nup002/Mathboard/hardware/pcb/kicad/resources/3d_models/xb-msk-103.stp

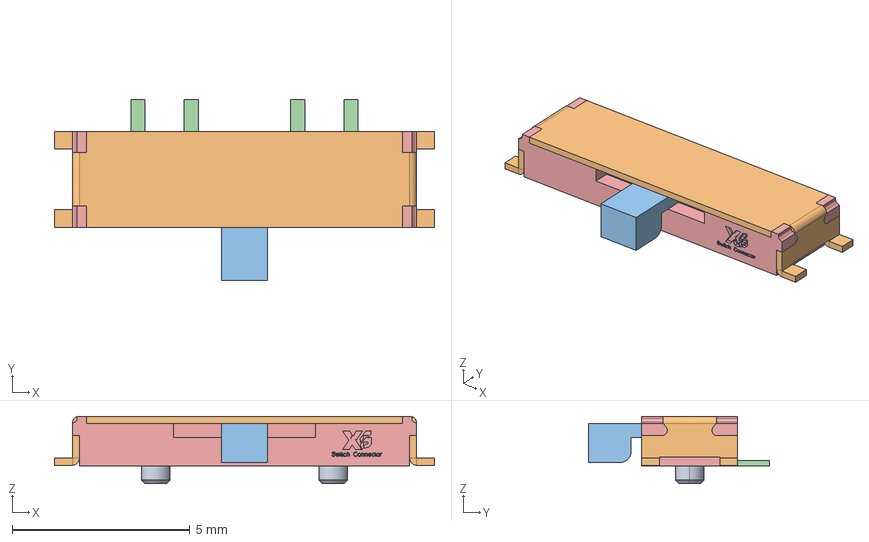
[picture p19: CAD file, 2024-10-21]
hardware/pcb/kicad/resources/3d_models/xb-msk-103.stp
10.7 x 5.10 x 1.90 mm
