nup002/Mathboard/hardware/pcb/kicad/resources/3d_models/3303W-3.step

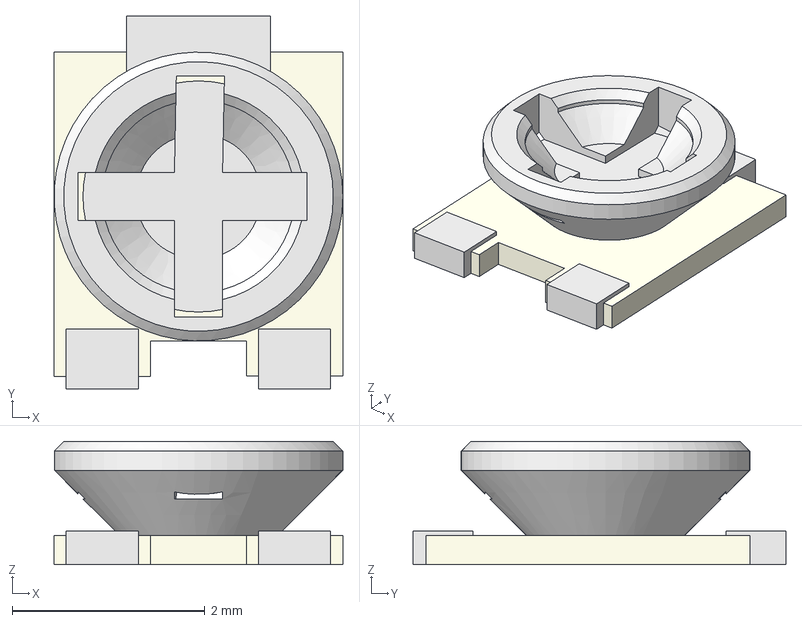
[picture p20: CAD file, 2024-10-21]
hardware/pcb/kicad/resources/3d_models/3303W-3.step
3.00 x 3.88 x 1.28 mm
