nup002/Mathboard/hardware/pcb/kicad/resources/3d_models/WSON8-8x6.STEP

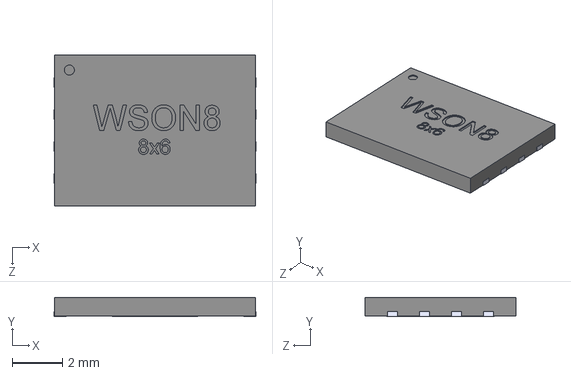
[picture p21: CAD file, 2024-10-21]
hardware/pcb/kicad/resources/3d_models/WSON8-8x6.STEP
8.02 x 0.77 x 6.00 mm
