nup002/Mathboard/hardware/pcb/kicad/resources/3d_models/USB - C inboard.STEP

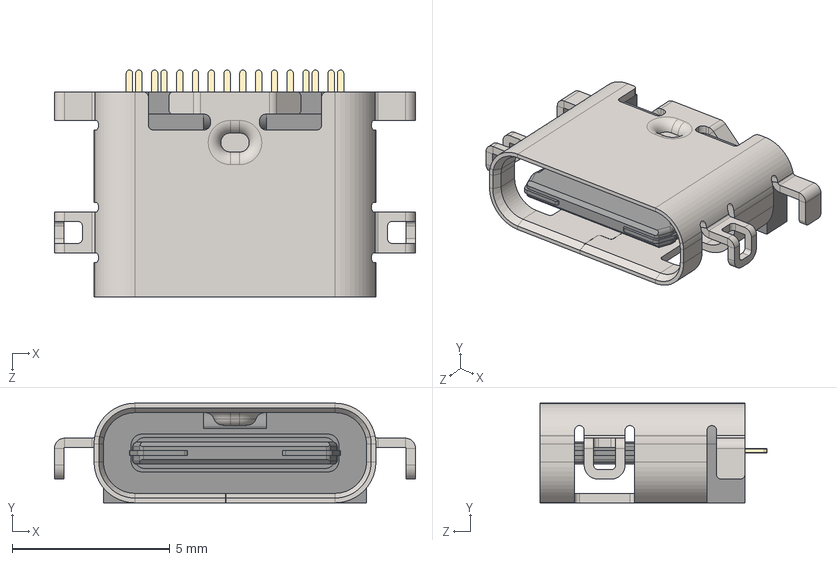
[picture p22: CAD file, 2024-10-01]
hardware/pcb/kicad/resources/3d_models/USB - C inboard.STEP
11.5 x 3.16 x 7.20 mm
USB-C inboard metal
USB-C plastic
