nup002/Mathboard/hardware/pcb/kicad/resources/3d_models/TS-1187A.step

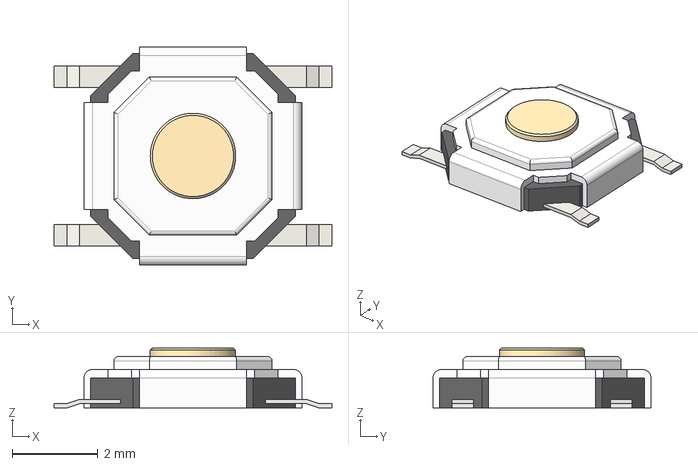
[picture p23: CAD file, 2024-09-27]
hardware/pcb/kicad/resources/3d_models/TS-1187A.step
6.50 x 5.10 x 1.40 mm
