nup002/Mathboard/hardware/pcb/kicad/resources/3d_models/SK6812MINI-E v1.step

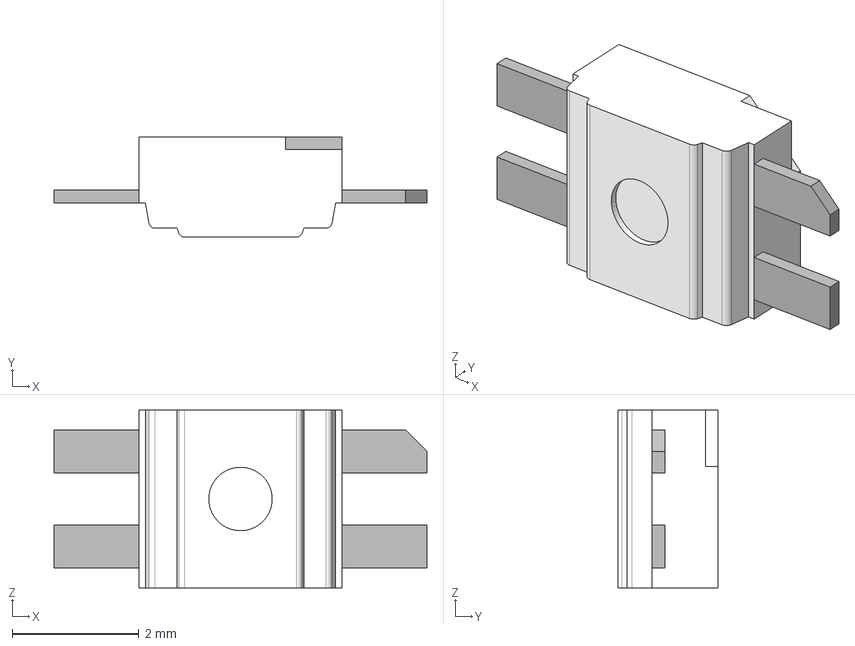
[picture p24: CAD file, 2024-04-30]
hardware/pcb/kicad/resources/3d_models/SK6812MINI-E v1.step
5.88 x 1.58 x 2.80 mm
