nup002/Mathboard/hardware/pcb/kicad/resources/3d_models/ks33.step

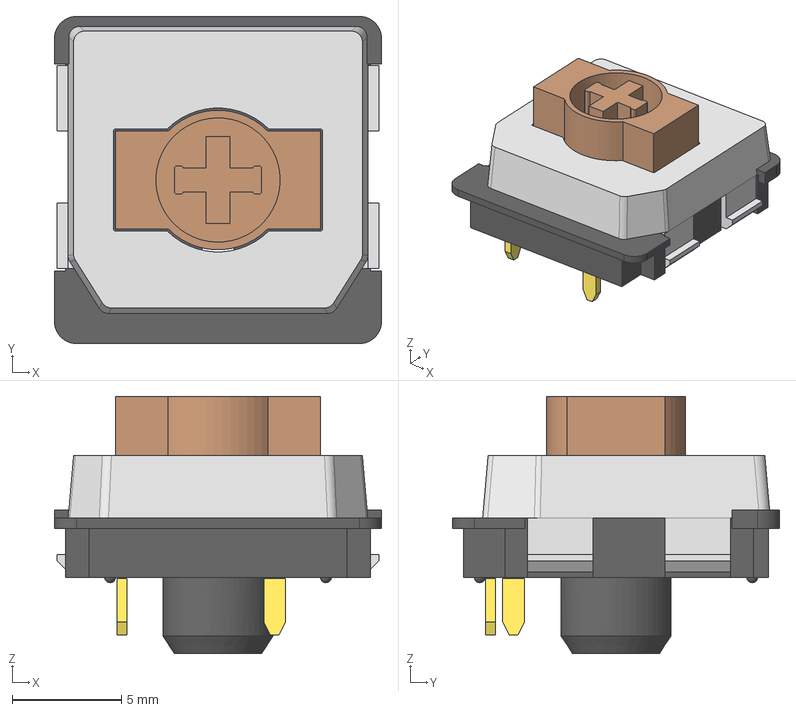
[picture p25: CAD file, 2023-12-31]
hardware/pcb/kicad/resources/3d_models/ks33.step
15.0 x 15.0 x 11.8 mm
f0684a6a-028c-11ee-ae0e-34c93d8226b1_part
f06a1f0c-028c-11ee-ae0e-34c93d8226b1_part
f1cc5b76-028c-11ee-ae0e-34c93d8226b1_part
f1cc5d06-028c-11ee-ae0e-34c93d8226b1_part
f1cc5d92-028c-11ee-ae0e-34c93d8226b1_part
