nup002/Mathboard/firmware/mathpad/v1/keymaps/default/keymap.c

/* Copyright 2024 Magne Lauritzen
 *
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
 * You should have received a copy of the GNU General Public License
 * along with this program.  If not, see <http://www.gnu.org/licenses/>.
 */
#include QMK_KEYBOARD_H
#include "globs.h"
#include "print.h"
#include "unicode_symbols.h"
#include "tapdance.h"
#include "microsoft_office.h"
#include "symbol_functions.h"

//#include "sendstring_norwegian.h"

#define _BASE 0         // left
#define _BASE_TOP 1     // top left
#define _BASE_BOTTOM 2  // bottom left
#define _OPT 3          // right
#define _OPT_TOP 4      // top right
#define _OPT_BOTTOM 5   // bottom right

// Sets the LED indicator to match the output mode
void update_led_to_match_mode(void) {
    switch (user_config.MODE) {
        case UC:
            rgblight_sethsv_at(HSV_CYAN, 0);
            break;
        case MOF:
            rgblight_sethsv_at(HSV_MAGENTA, 0);
            break;
        case LTX:
            rgblight_sethsv_at(HSV_YELLOW, 0);
            break;
    }
}

// Sets the mathpad output mode
void output_mode_set(uint8_t mode) { 
    user_config.MODE = mode; 
    eeconfig_update_user(user_config.raw);
    update_led_to_match_mode();
}

// Cycles between mathpad output modes when called. UC -> MOF -> LTX -> UC
void output_mode_update(void) {
    if (user_config.MODE == UC){output_mode_set(MOF);} 
    else if (user_config.MODE == MOF){output_mode_set(LTX);}
    else if (user_config.MODE == LTX){output_mode_set(UC);}
}

// The custom_keycodes define all the "normal", or non-tapdance, symbols of the mathpad. These are the symbols that 
// (on the Matboard) do not have a red dot next to them. Examples include the nearly equal sign, nabla, and arrows. 
// Tapdance symbols are those symbols which have different behaviour depending on how many times you tap them. They have
// red dots next to them on the Matboard. These symbols are defined in the file tapdance.h.
enum custom_keycodes {
    KC_SWITCH_MODE = SAFE_RANGE, // KC_SWITCH_MODE is a special button that cycles the mathpad MODE variable.
    KC_ALPHA,
    KC_NOTEQUAL,
    KC_BETA,
    KC_ALMOSTEQUAL,
    KC_ACCENT_CIRCUMFLEX,
    KC_ACCENT_CHECK,
    KC_PROPORTIONAL,
    KC_IDENTICALTO,
    KC_COMBININGTILDE,
    KC_COMBININGBAR,
    KC_EPSILON,
    KC_LESSOREQUAL,
    KC_ZETA,
    KC_GREATEROREQUAL,
    KC_ACCENT_ARROW,
    KC_ETA,
    KC_IOTA,
    KC_SUM,
    KC_KAPPA,
    KC_NARYPRODUCT,
    KC_UNION,
    KC_INTERSECTION,
    KC_MU,
    KC_EMPTYSET,
    KC_NU,
    KC_ARROW,
    KC_SETDIFFERENCE,
    KC_OMICRON,
    KC_PARTIALDERIVATIVE,
    KC_NABLA,
    KC_DISJOINTUNION,
    KC_RHO,
    KC_ARROWIMPLIES,
    KC_ARROWIFANDONLYIF,
    KC_DOTPRODUCT,
    KC_CROSSPRODUCT,
    KC_TAU,
    KC_UPSILON,
    KC_PARALLEL,
    KC_FORALL,
    KC_CHI,
    KC_DEGREE,
    KC_INFINITY,
    KC_NOT,
    KC_MATRIX,
    KC_FRACTION
};

// Each physical symbolkey on the mathpad is defined here. The upper rightmost key is 00. The bottommost key is 23:
// 00 01 02 03 <- Top row
// 10 11 12 13 <- Middle row
// 20 21 22 23 <- Bottom row
// The index of a symbol in key arrays defines its location on the physical key. It goes:
// [left, top left, bottom left, right, top right, bottom right] 
const int key00[6] = {KC_ALPHA, KC_NOTEQUAL, KC_ACCENT_CIRCUMFLEX, KC_BETA, KC_ALMOSTEQUAL, KC_ACCENT_CHECK};
const int key01[6] = {TD(GAMMA_TD), KC_PROPORTIONAL, KC_COMBININGTILDE, TD(DELTA_TD), KC_IDENTICALTO, KC_COMBININGBAR};
const int key02[6] = {KC_EPSILON, KC_LESSOREQUAL, KC_ACCENT_ARROW, KC_ZETA, KC_GREATEROREQUAL, TD(DOT_TD)};
const int key03[6] = {KC_ETA, TD(MLT_TD), TD(SUB_TD), TD(THETA_TD), TD(MGT_TD), TD(SUP_TD)};
const int key10[6] = {KC_IOTA, KC_SUM, KC_UNION, KC_KAPPA, KC_NARYPRODUCT, KC_INTERSECTION};
const int key11[6] = {TD(LAMBDA_TD), TD(INTEGRAL_TD), TD(ELEMENT_OF_TD), KC_MU, TD(LINE_INTEGRAL_TD), KC_EMPTYSET};
const int key12[6] = {KC_NU, TD(ROOT_TD), TD(SUBSET_OF_TD), TD(XI_TD), KC_ARROW, KC_SETDIFFERENCE};
const int key13[6] = {KC_OMICRON, KC_PARTIALDERIVATIVE, TD(SUBSET_OR_EQ_TD), TD(PI_TD), KC_NABLA, KC_DISJOINTUNION};
const int key20[6] = {KC_RHO, KC_ARROWIMPLIES, KC_DOTPRODUCT, TD(SIGMA_TD), KC_ARROWIFANDONLYIF, KC_CROSSPRODUCT};
const int key21[6] = {KC_TAU, TD(THERE_EXIST_TD), TD(PLUSMINUS_TD), KC_UPSILON, TD(AND_TD), KC_PARALLEL};
const int key22[6] = {TD(PHI_TD), KC_FORALL, KC_DEGREE, KC_CHI, TD(UNCONDITIONALLY_TRUE_TD), KC_INFINITY};
const int key23[6] = {TD(PSI_TD), KC_NOT, KC_MATRIX, TD(OMEGA_TD), TD(PROVES_TD), KC_FRACTION};


// process_record_user handles keyclicks on "normal" (non-tapdance) symbols. Each normal symbol has a function defined in 
// symbol_functions.h. For example, when the user clicks KC_NOTEQUAL, process_record_user() will call notequal_key(). 
// The symbol functions defined in symbol_functions.h decides which action to take depending on the mathpad MODE.
bool process_record_user(uint16_t keycode, keyrecord_t *record) {
    switch (keycode) {
        case KC_SWITCH_MODE:
            if (record->event.pressed) {
                output_mode_update();
            }
            break;
        case KC_ALPHA:
            alpha_key(record);
            break;
        case KC_NOTEQUAL:
            notequal_key(record);
            break;
        case KC_BETA:
            beta_key(record);
            break;
        case KC_ALMOSTEQUAL:
            almostequal_key(record);
            break;
        case KC_ACCENT_CIRCUMFLEX:
            circumflex_key(record);
            break;
        case KC_ACCENT_CHECK:
            check_key(record);
            break;
        case KC_PROPORTIONAL:
            proportional_key(record);
            break;
        case KC_IDENTICALTO:
            identicalto_key(record);
            break;
        case KC_COMBININGTILDE:
            combiningtilde_key(record);
            break;
        case KC_COMBININGBAR:
            combiningbar_key(record);
            break;
        case KC_EPSILON:
            epsilon_key(record);
            break;
        case KC_LESSOREQUAL:
            lessorequal_key(record);
            break;
        case KC_ZETA:
            zeta_key(record);
            break;
        case KC_GREATEROREQUAL:
            greaterorequal_key(record);
            break;
        case KC_ACCENT_ARROW:
            accent_arrow_key(record);
            break;
        case KC_ETA:
            eta_key(record);
            break;
        case KC_IOTA:
            iota_key(record);
            break;
        case KC_SUM:
            sum_key(record);
            break;
        case KC_KAPPA:
            kappa_key(record);
            break;
        case KC_NARYPRODUCT:
            naryproduct_key(record);
            break;
        case KC_UNION:
            union_key(record);
            break;
        case KC_INTERSECTION:
            intersection_key(record);
            break;
        case KC_MU:
            mu_key(record);
            break;
        case KC_EMPTYSET:
            emptyset_key(record);
            break;
        case KC_NU:
            nu_key(record);
            break;
        case KC_ARROW:
            arrow_key(record);
            break;
        case KC_SETDIFFERENCE:
            setdifference_key(record);
            break;
        case KC_OMICRON:
            omicron_key(record);
            break;
        case KC_PARTIALDERIVATIVE:
            partialderivative_key(record);
            break;
        case KC_NABLA:
            nabla_key(record);
            break;
        case KC_DISJOINTUNION:
            disjointunion_key(record);
            break;
        case KC_RHO:
            rho_key(record);
            break;
        case KC_ARROWIMPLIES:
            arrowimplies_key(record);
            break;
        case KC_ARROWIFANDONLYIF:
            arrowifandonlyif_key(record);
            break;
        case KC_DOTPRODUCT:
            dotproduct_key(record);
            break;
        case KC_CROSSPRODUCT:
            crossproduct_key(record);
            break;
        case KC_TAU:
            tau_key(record);
            break;
        case KC_UPSILON:
            upsilon_key(record);
            break;
        case KC_PARALLEL:
            parallel_key(record);
            break;
        case KC_FORALL:
            forall_key(record);
            break;
        case KC_CHI:
            chi_key(record);
            break;
        case KC_DEGREE:
            degree_key(record);
            break;
        case KC_INFINITY:
            infinity_key(record);
            break;
        case KC_NOT:
            not_key(record);
            break;
        case KC_FRACTION:
            fraction_key(record);
            break;
        case KC_MATRIX:
            matrix_key(record);
            break;
    }
    return true;
};


layer_state_t layer_state_set_user(layer_state_t state) {
    print("\n\n==== layer_state_set_user called ====\n");
    
    char layer_info[128];
    sprintf(layer_info, "Initial state: %d\n", state);
    print(layer_info);
    
    // Check if either of our special layers is already active
    bool opt_bottom_active = IS_LAYER_ON_STATE(state, _OPT_BOTTOM);
    bool opt_top_active = IS_LAYER_ON_STATE(state, _OPT_TOP);
    
    print("Layer Status: ");
    if (IS_LAYER_ON_STATE(state, _OPT)) print("OPT:ON ");
    else print("OPT:OFF ");
    
    if (IS_LAYER_ON_STATE(state, _BASE_BOTTOM)) print("BASE_BOTTOM:ON ");
    else print("BASE_BOTTOM:OFF ");
    
    if (IS_LAYER_ON_STATE(state, _BASE_TOP)) print("BASE_TOP:ON ");
    else print("BASE_TOP:OFF ");
    
    if (opt_bottom_active) print("OPT_BOTTOM:ON ");
    else print("OPT_BOTTOM:OFF ");
    
    if (opt_top_active) print("OPT_TOP:ON ");
    else print("OPT_TOP:OFF ");
    print("\n");
    
    // If OPT_BOTTOM is active, any press of BASE_TOP should be ignored
    if (opt_bottom_active && IS_LAYER_ON_STATE(state, _BASE_TOP)) {
        print("OPT_BOTTOM is active, ignoring BASE_TOP press\n");
        state = state & ~(1UL << _BASE_TOP);
        sprintf(layer_info, "State after ignoring BASE_TOP: %d\n", state);
        print(layer_info);
    }
    
    // If OPT_TOP is active, any press of BASE_BOTTOM should be ignored
    if (opt_top_active && IS_LAYER_ON_STATE(state, _BASE_BOTTOM)) {
        print("OPT_TOP is active, ignoring BASE_BOTTOM press\n");
        state = state & ~(1UL << _BASE_BOTTOM);
        sprintf(layer_info, "State after ignoring BASE_BOTTOM: %d\n", state);
        print(layer_info);
    }
    
    // Check for invalid combinations (BASE_TOP+BASE_BOTTOM without any active special layers)
    bool base_bottom_layer_on = IS_LAYER_ON_STATE(state, _BASE_BOTTOM);
    bool base_top_layer_on = IS_LAYER_ON_STATE(state, _BASE_TOP);
    
    if (base_bottom_layer_on && base_top_layer_on && !opt_bottom_active && !opt_top_active) {
        print("Invalid combination (BASE_TOP+BASE_BOTTOM), returning to base layer\n");
        return 0;
    }
    
    // Now handle the tri-layer states with the modified state
    print("Checking tri-layer combinations\n");
    
    layer_state_t opt_bottom_state = update_tri_layer_state(state, _OPT, _BASE_BOTTOM, _OPT_BOTTOM);
    if (opt_bottom_state != state) {
        print("Activating OPT_BOTTOM layer\n");
        sprintf(layer_info, "New state: %d\n", opt_bottom_state);
        print(layer_info);
    }
    
    layer_state_t opt_top_state = update_tri_layer_state(state, _OPT, _BASE_TOP, _OPT_TOP);
    if (opt_top_state != state) {
        print("Activating OPT_TOP layer\n");
        sprintf(layer_info, "New state: %d\n", opt_top_state);
        print(layer_info);
    }
    
    // Return the appropriate state
    if (opt_bottom_state != state) {
        print("Returning OPT_BOTTOM state\n");
        print("==== End of function ====\n");
        return opt_bottom_state;
    } else if (opt_top_state != state) {
        print("Returning OPT_TOP state\n");
        print("==== End of function ====\n");
        return opt_top_state;
    } else {
        print("Returning unchanged state\n");
        print("==== End of function ====\n");
        return state;
    }
}

const uint16_t PROGMEM keymaps[][MATRIX_ROWS][MATRIX_COLS] = {
    [_BASE] = LAYOUT_5x3_macropad(
        key00[_BASE], key01[_BASE],   key02[_BASE],   key03[_BASE],   KC_SWITCH_MODE,
                      key10[_BASE],   key11[_BASE],   key12[_BASE],   key13[_BASE],
        MO(_OPT),     key20[_BASE],   key21[_BASE],   key22[_BASE],   key23[_BASE],
                                      MO(_BASE_BOTTOM),                MO(_BASE_TOP)
    ),
	[_BASE_TOP] = LAYOUT_5x3_macropad(
        key00[_BASE_TOP], key01[_BASE_TOP],   key02[_BASE_TOP],   key03[_BASE_TOP],   KC_NO,
                          key10[_BASE_TOP],   key11[_BASE_TOP],   key12[_BASE_TOP],   key13[_BASE_TOP],
        MO(_OPT),         key20[_BASE_TOP],   key21[_BASE_TOP],   key22[_BASE_TOP],   key23[_BASE_TOP],
                                              MO(_BASE_BOTTOM),                       MO(_BASE_TOP)
    ),
	[_OPT] = LAYOUT_5x3_macropad(
        key00[_OPT], key01[_OPT],   key02[_OPT],   key03[_OPT],   KC_NO,
                     key10[_OPT],   key11[_OPT],   key12[_OPT],   key13[_OPT],
        MO(_OPT),    key20[_OPT],   key21[_OPT],   key22[_OPT],   key23[_OPT],
                                    MO(_BASE_BOTTOM),             MO(_BASE_TOP)
    ),
	[_OPT_TOP] = LAYOUT_5x3_macropad(
        key00[_OPT_TOP], key01[_OPT_TOP],   key02[_OPT_TOP],   key03[_OPT_TOP],   KC_NO,
                         key10[_OPT_TOP],   key11[_OPT_TOP],   key12[_OPT_TOP],   key13[_OPT_TOP],
        MO(_OPT),        key20[_OPT_TOP],   key21[_OPT_TOP],   key22[_OPT_TOP],   key23[_OPT_TOP],
                                            MO(_BASE_BOTTOM),                     MO(_BASE_TOP)
    ),
	[_BASE_BOTTOM] = LAYOUT_5x3_macropad(
        key00[_BASE_BOTTOM], key01[_BASE_BOTTOM],   key02[_BASE_BOTTOM],   key03[_BASE_BOTTOM],   KC_NO,
                             key10[_BASE_BOTTOM],   key11[_BASE_BOTTOM],   key12[_BASE_BOTTOM],   key13[_BASE_BOTTOM],
        MO(_OPT),            key20[_BASE_BOTTOM],   key21[_BASE_BOTTOM],   key22[_BASE_BOTTOM],   key23[_BASE_BOTTOM],
                                                    MO(_BASE_BOTTOM),                             MO(_BASE_TOP)
    ),
	[_OPT_BOTTOM] = LAYOUT_5x3_macropad(
        key00[_OPT_BOTTOM], key01[_OPT_BOTTOM],   key02[_OPT_BOTTOM],   key03[_OPT_BOTTOM],   KC_NO,
                            key10[_OPT_BOTTOM],   key11[_OPT_BOTTOM],   key12[_OPT_BOTTOM],   key13[_OPT_BOTTOM],
        MO(_OPT),           key20[_OPT_BOTTOM],   key21[_OPT_BOTTOM],   key22[_OPT_BOTTOM],   key23[_OPT_BOTTOM],
                                                  MO(_BASE_BOTTOM),                           MO(_BASE_TOP)
    )
};

bool dip_switch_update_user(uint8_t index, bool active) { 
    // active = !active; // uncomment for pcb rev 1
    uint8_t current_unicode_mode = get_unicode_input_mode();
    switch (index) {
        case 0:
            if(active & (current_unicode_mode!=UNICODE_MODE_LINUX)) {
                set_unicode_input_mode(UNICODE_MODE_LINUX); 
                }
            break;
        case 1:
            if(active & (current_unicode_mode!=UNICODE_MODE_MACOS)) {
                set_unicode_input_mode(UNICODE_MODE_MACOS); 
                }
            break;
        case 2:
            if(active & (current_unicode_mode!=UNICODE_MODE_WINCOMPOSE)) {
                set_unicode_input_mode(UNICODE_MODE_WINCOMPOSE); 
                }
            break;
    }
    return true;
};

void keyboard_post_init_user(void) {
  user_config.raw = eeconfig_read_user(); // Read the user config from EEPROM
  update_led_to_match_mode();
}

// DEBUG THINGS

void unicode_input_mode_set_user(uint8_t input_mode) {
    return;  // Comment this return statement to print a message when the unicode mode changes
    send_string(" Switched to unicode mode : ");
    switch (input_mode) {
        case UNICODE_MODE_LINUX:
            send_string("UNICODE_MODE_LINUX");
            break;
        case UNICODE_MODE_MACOS:
            send_string("UNICODE_MODE_MACOS");
            break;
        case UNICODE_MODE_WINCOMPOSE:
            send_string("UNICODE_MODE_WINCOMPOSE");
            break;
    }
};
