nup002/Mathboard/firmware/mathpad/mp1a/keymaps/default/modifiers.c

/* Copyright 2025 Summacogni OU
 *
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
 * You should have received a copy of the GNU General Public License
 * along with this program.  If not, see <http://www.gnu.org/licenses/>.
 */

 #include "info.h"
#include QMK_KEYBOARD_H
 #include "modifiers.h"
 #include "globals.h"
 
 // Initiate the modifier key states to false on Mathpad boot
 bool rightkey_toggled = false;
 bool midkey_toggled = false;
 bool bottomkey_toggled = false;
 bool rightkey_pressed = false;
 bool midkey_pressed = false;
 bool bottomkey_pressed = false;
 
 
 /**
  * @brief Function to update active layer based on modifier states
  *
  * This function must be called each time a modifier key is pressed or released.
  * It will update the active layer based on the modifier key states.
  */
 void update_active_layer(void) {
     static uint16_t debug_info_timer;
     
     layer_clear(); // Clear all layers first
 
     // Set the appropriate layer based on modifier key combinations
     if (rightkey_toggled && bottomkey_toggled && !midkey_toggled) {
         layer_on(_RIGHT_BOTTOM); // RIGHT and FRONT modifier keys are pressed
     } else if (rightkey_toggled && midkey_toggled && !bottomkey_toggled) {
         layer_on(_RIGHT_CENTER); // RIGHT and MIDDLE keys are pressed
     } else if (rightkey_toggled && !midkey_toggled && !bottomkey_toggled) {
         layer_on(_RIGHT_TOP); // Only RIGHT key is pressed
     } else if (!rightkey_toggled && midkey_toggled && !bottomkey_toggled) {
         layer_on(_LEFT_CENTER); // Only MIDDLE key is pressed
     } else if (!rightkey_toggled && !midkey_toggled && bottomkey_toggled) {
         layer_on(_LEFT_BOTTOM); // Only FRONT key is pressed
     } else {
         layer_on(_LEFT_TOP); // Default or invalid combinations go to the default _LEFT_TOP
     }
     
     // If the user has been holding down all modifier keys for a long time, we print debug info
     if (debug_info_timer != 0) {
        uint16_t time_delta = timer_read() - debug_info_timer;
        debug_info_timer = 0;
        if (time_delta > 5000){  // Print debug info after 5 seconds
            print_info();
        }
     }
 
     bool all_modifier_keys_pressed = rightkey_pressed && midkey_pressed && bottomkey_pressed;
     if (all_modifier_keys_pressed){
         // The user is pressing all modifier keys. We start the debug info print timer.
         debug_info_timer = timer_read();
     }
 }
 
