nup002/Mathboard/firmware/mathpad/mp1a/keymaps/default/multitap.h

/* Copyright 2025 Summacogni OU
 *
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
 * You should have received a copy of the GNU General Public License
 * along with this program.  If not, see <http://www.gnu.org/licenses/>.
 */

#ifndef MULTITAP_H
#define MULTITAP_H

#include QMK_KEYBOARD_H
#include "symbols/symbols.h"

// Helper function to handle tap dance actions
void symbol_dance(tap_dance_state_t *s, void *d, const symbol_definition_t **symbols, uint8_t symbol_count);

// Greek symbols
void gamma_dance(tap_dance_state_t *s, void *d);
void delta_dance(tap_dance_state_t *s, void *d);
void theta_dance(tap_dance_state_t *s, void *d);
void lambda_dance(tap_dance_state_t *s, void *d);
void xi_dance(tap_dance_state_t *s, void *d);
void pi_dance(tap_dance_state_t *s, void *d);
void sigma_dance(tap_dance_state_t *s, void *d);
void varphi_dance(tap_dance_state_t *s, void *d);
void psi_dance(tap_dance_state_t *s, void *d);
void omega_dance(tap_dance_state_t *s, void *d);

// Comparison symbols
void asymptotically_equal_dance(tap_dance_state_t *s, void *d);
void identically_equal_dance(tap_dance_state_t *s, void *d);
void equal_by_definition_dance(tap_dance_state_t *s, void *d);
void greater_or_equal_dance(tap_dance_state_t *s, void *d);
void much_greater_than_dance(tap_dance_state_t *s, void *d);

// Accents and sub/sup symbols
void accent_dot_dance(tap_dance_state_t *s, void *d);
void sub_dance(tap_dance_state_t *s, void *d);
void sup_dance(tap_dance_state_t *s, void *d);

// Calculus symbols
void integral_dance(tap_dance_state_t *s, void *d);
void line_integral_dance(tap_dance_state_t *s, void *d);

// Algebra symbols
void root_dance(tap_dance_state_t *s, void *d);

// Arrows
void arrow_dance(tap_dance_state_t *s, void *d);
void double_arrow_dance(tap_dance_state_t *s, void *d);

// Set theory symbols
void union_dance(tap_dance_state_t *s, void *d);
void empty_set_dance(tap_dance_state_t *s, void *d);
void element_of_dance(tap_dance_state_t *s, void *d);
void proper_subset_dance(tap_dance_state_t *s, void *d);
void subset_dance(tap_dance_state_t *s, void *d);

//Logic symbols
void there_exists_dance(tap_dance_state_t *s, void *d);
void and_dance(tap_dance_state_t *s, void *d);
void down_tack_dance(tap_dance_state_t *s, void *d);

// Misc symbols
void circled_plus_dance(tap_dance_state_t *s, void *d);
void times_dance(tap_dance_state_t *s, void *d);
void plusminus_dance(tap_dance_state_t *s, void *d);

#endif // MULTITAP_H
