nup002/Mathboard/firmware/mathpad/mp1a/keymaps/default/mode.c

/* Copyright 2025 Summacogni OU
 *
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
 * You should have received a copy of the GNU General Public License
 * along with this program.  If not, see <http://www.gnu.org/licenses/>.
 */

// Functions related to setting the 'mode' of the Mathpad, meaning which 
// representation is used when typing symbols. Modes include Unicode, 
// LaTeX, Microsoft Office Equation Editor, and soon LibreOffice.

#include "mode.h"
#include QMK_KEYBOARD_H
#include "globals.h"

/** 
* When 'update_led_to_match_mode' is called, it checks the current value of
* user_config.MODE and sets the mode key backlight to the
* corresponding color.
* 
* The colors are defined as follows:
* - UC_MODE:  White     (Unicode)
* - MOF_MODE: Magenta   (Microsoft Office Equation Editor)
* - LTX_MODE: Yellow    (LaTeX)
*/
void update_led_to_match_mode(void) {
    switch (user_config.MODE) {
        case UC_MODE:
            rgblight_sethsv_at(HSV_WHITE, 0);
            break;
        case MOF_MODE:
            rgblight_sethsv_at(HSV_MAGENTA, 0);
            break;
        case LTX_MODE:
            rgblight_sethsv_at(HSV_YELLOW, 0);
            break;
    }
}


/**
 * Sets the mathpad output mode.
 *
 * This function updates the user configuration with the specified mode,
 * writes the configuration back persistent memory, and updates the LED to reflect
 * the current mode.
 *
 * @param mode The mode to set. This should be one of the predefined modes
 *             such as UC_MODE, MOF_MODE, or LTX_MODE defined in mode.h
 */
void output_mode_set(uint8_t mode) { 
    user_config.MODE = mode; 
    eeconfig_update_user(user_config.raw); 
    update_led_to_match_mode();
}


/**
 * Cycles between mathpad output modes when called. 
 * It goes UC_MODE -> MOF_MODE -> LTX_MODE -> UC_MODE
 * 
 * This function is meant to be called from the keymap to cycle the output
 * modes of the mathpad.
 */
void output_mode_update(void) {
    if (user_config.MODE == UC_MODE) {
        output_mode_set(MOF_MODE);
    } else if (user_config.MODE == MOF_MODE) {
        output_mode_set(LTX_MODE);
    } else if (user_config.MODE == LTX_MODE) {
        output_mode_set(UC_MODE);
    }
}
